eutectic6337/soldering-exercise/i/PCB back.jpg

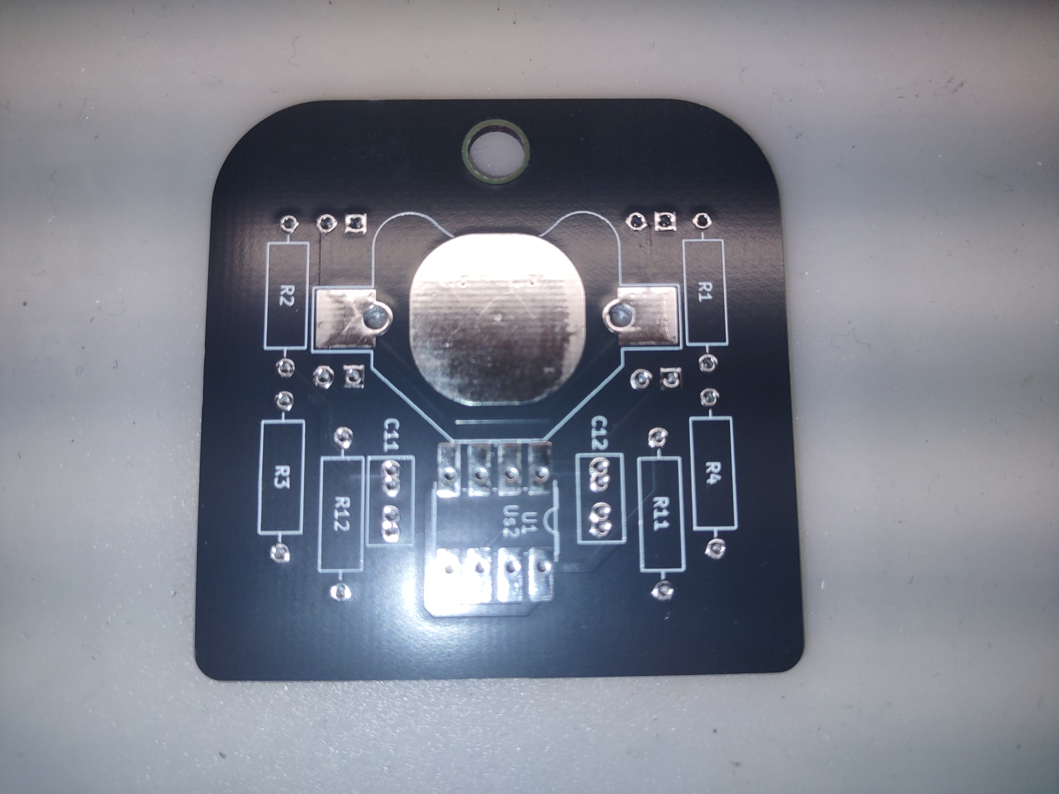
i/PCB back.jpg
