eutectic6337/soldering-exercise/i/PCB front.jpg

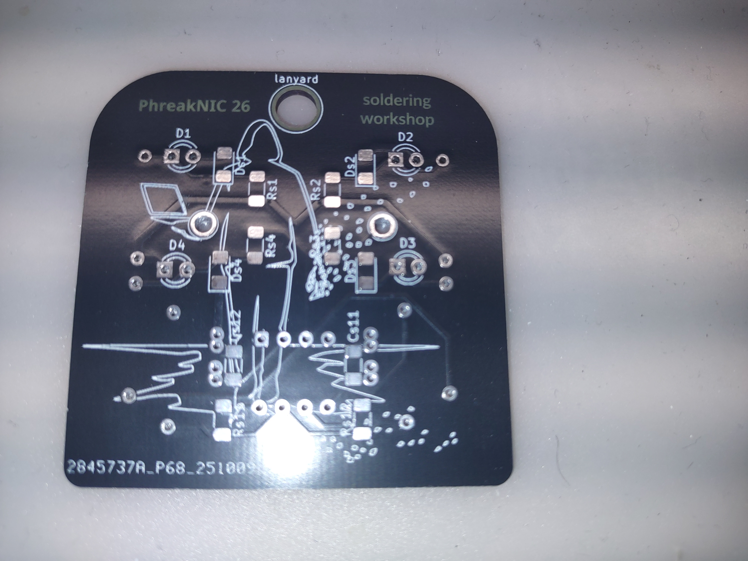
i/PCB front.jpg
