eutectic6337/soldering-exercise/i/SMD 555 front.png

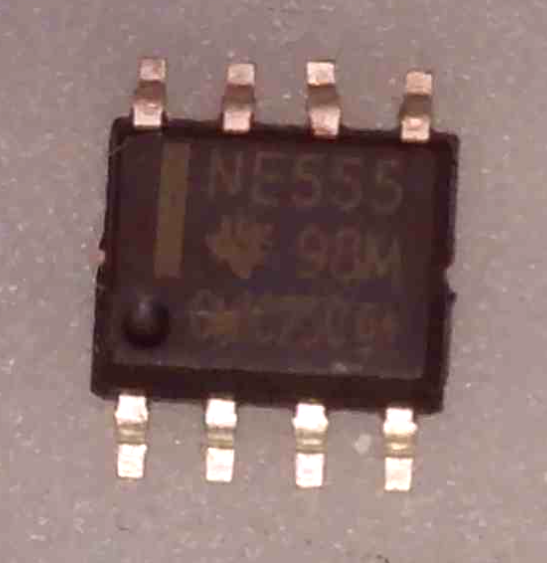
i/SMD 555 front.png
