eutectic6337/soldering-exercise/i/SMD 555 side.png

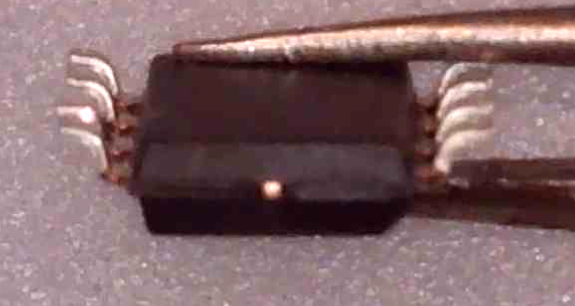
i/SMD 555 side.png
