eutectic6337/soldering-exercise/i/SMD 555 tape.png

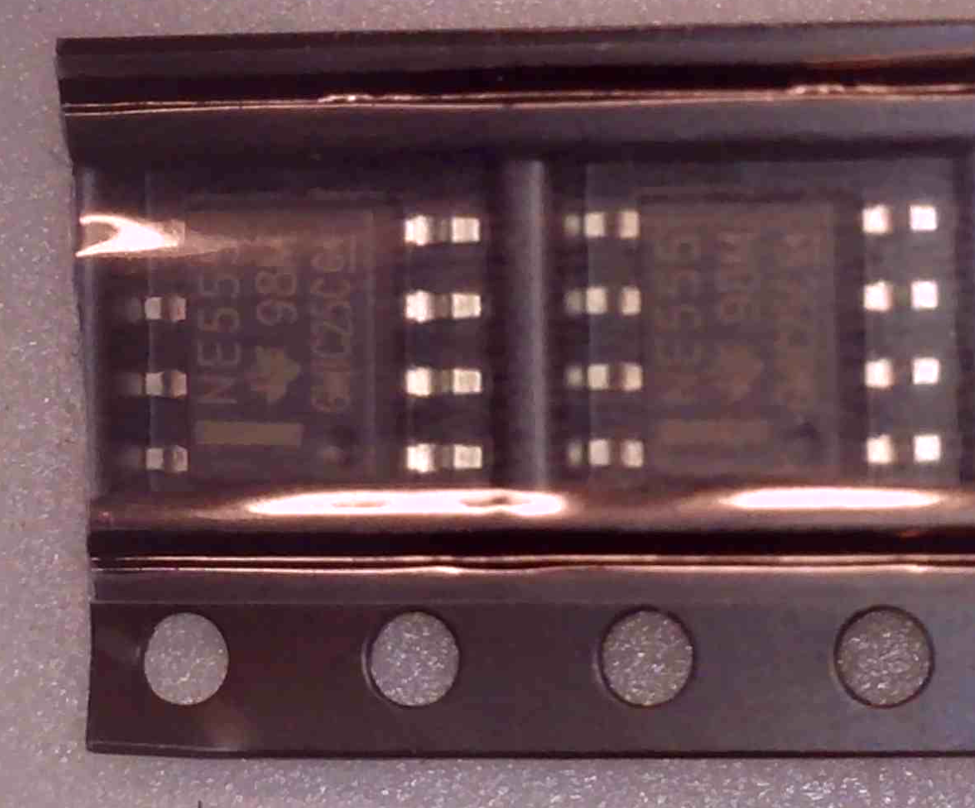
i/SMD 555 tape.png
