eutectic6337/soldering-exercise/i/SMD LED angled.png

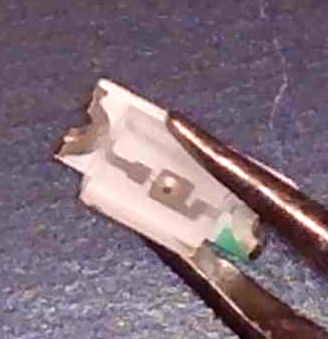
i/SMD LED angled.png
