eutectic6337/soldering-exercise/i/SMD LED back.png

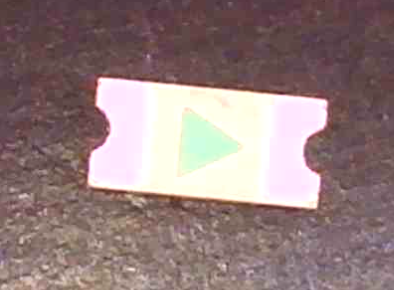
i/SMD LED back.png
