eutectic6337/soldering-exercise/i/SMD LED front.png

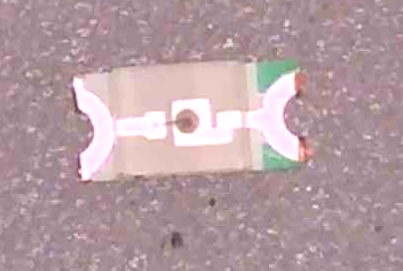
i/SMD LED front.png
