eutectic6337/soldering-exercise/i/SMD LED side.png

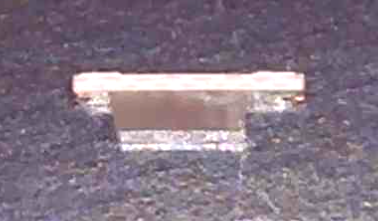
i/SMD LED side.png
