eutectic6337/soldering-exercise/i/SMD resistor 22R tape.png

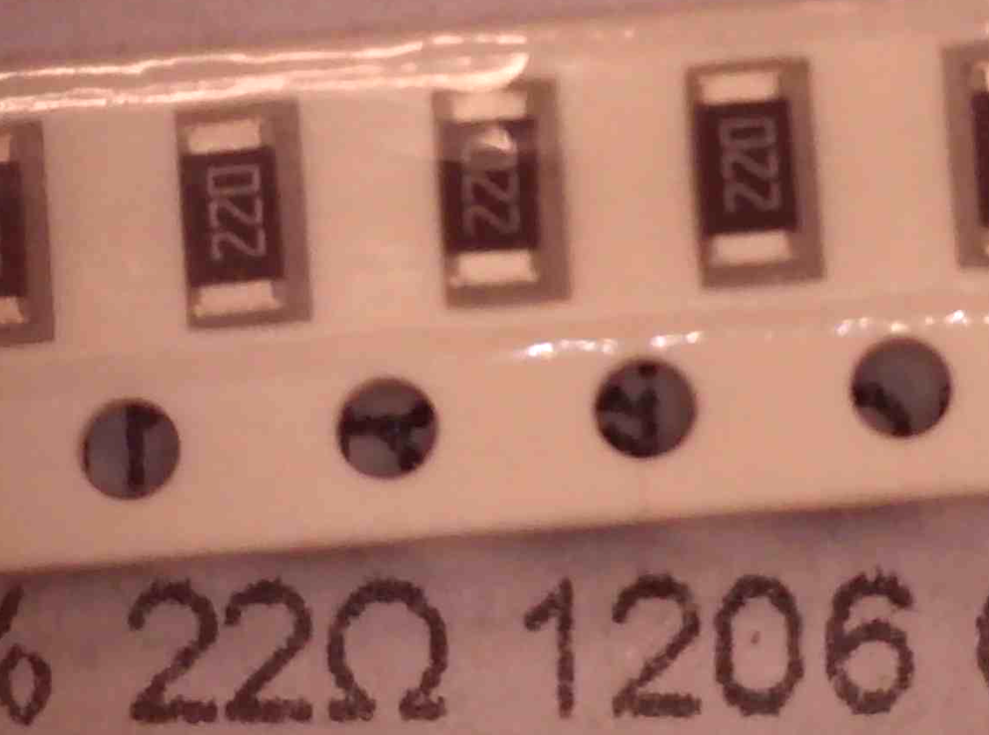
i/SMD resistor 22R tape.png
