eutectic6337/soldering-exercise/i/SMD resistor 62R front.png

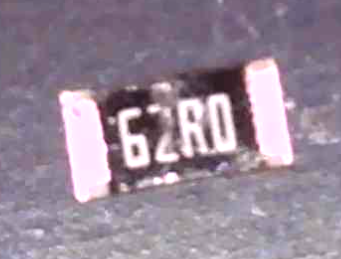
i/SMD resistor 62R front.png
