eutectic6337/soldering-exercise/i/SMD resistor 62R tape.png

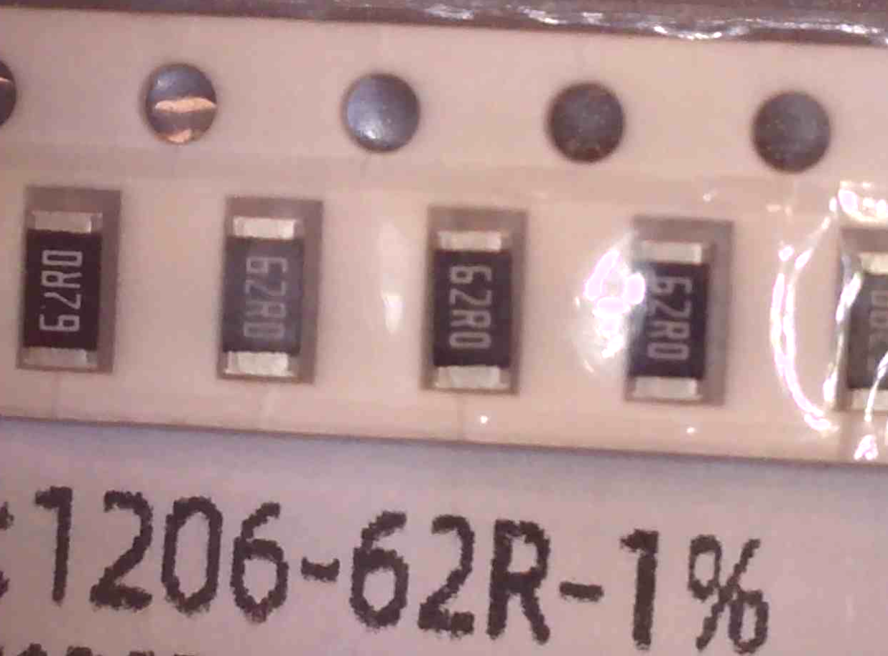
i/SMD resistor 62R tape.png
