eutectic6337/soldering-exercise/i/SMD resistor back.png

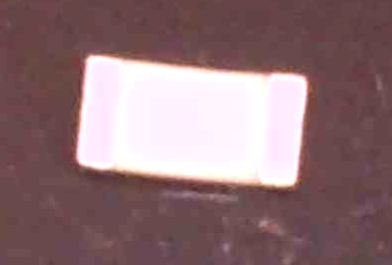
i/SMD resistor back.png
