eutectic6337/soldering-exercise/i/SMD resistor side.png

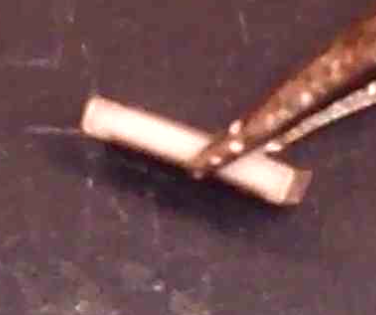
i/SMD resistor side.png
