eutectic6337/soldering-exercise/i/THT 555 front.png

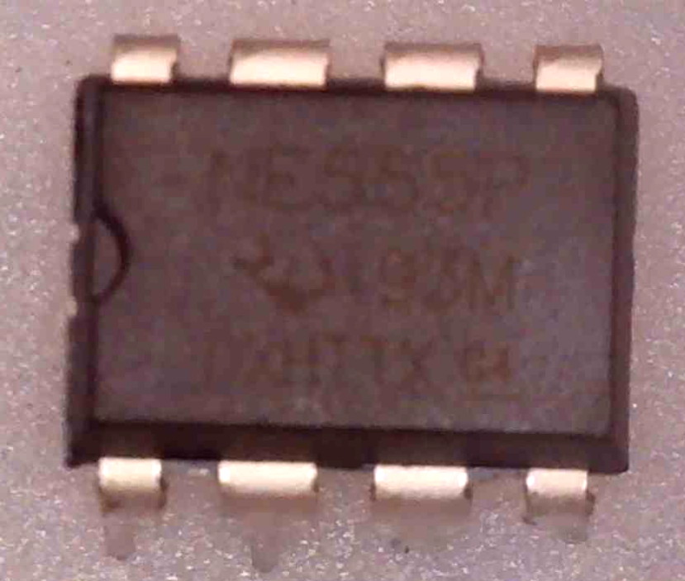
i/THT 555 front.png
