eutectic6337/soldering-exercise/i/THT 555 side.png

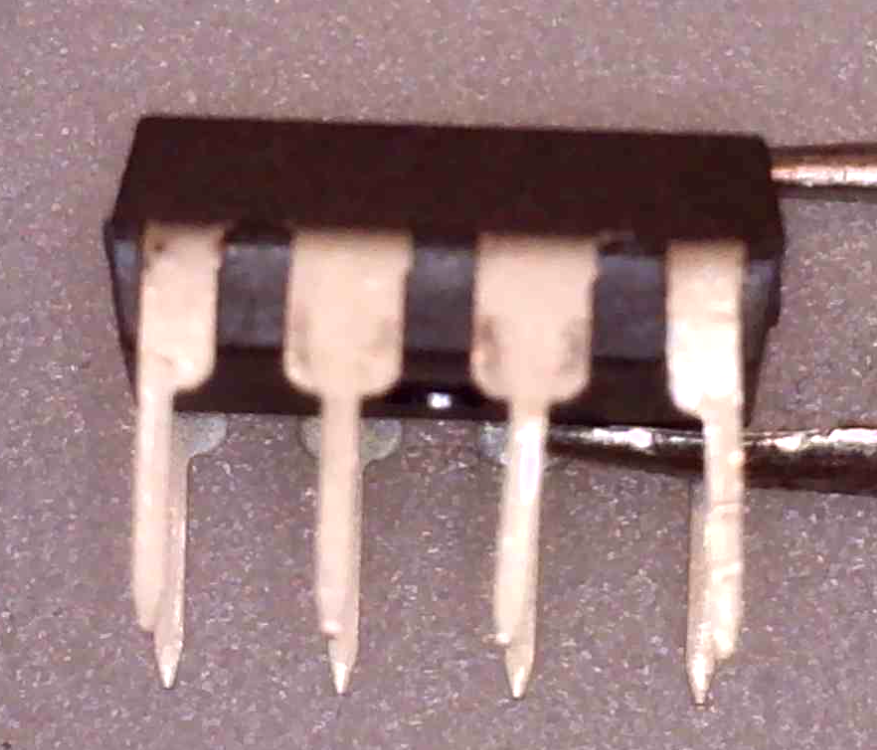
i/THT 555 side.png
