eutectic6337/soldering-exercise/i/THT LED blue.jpg

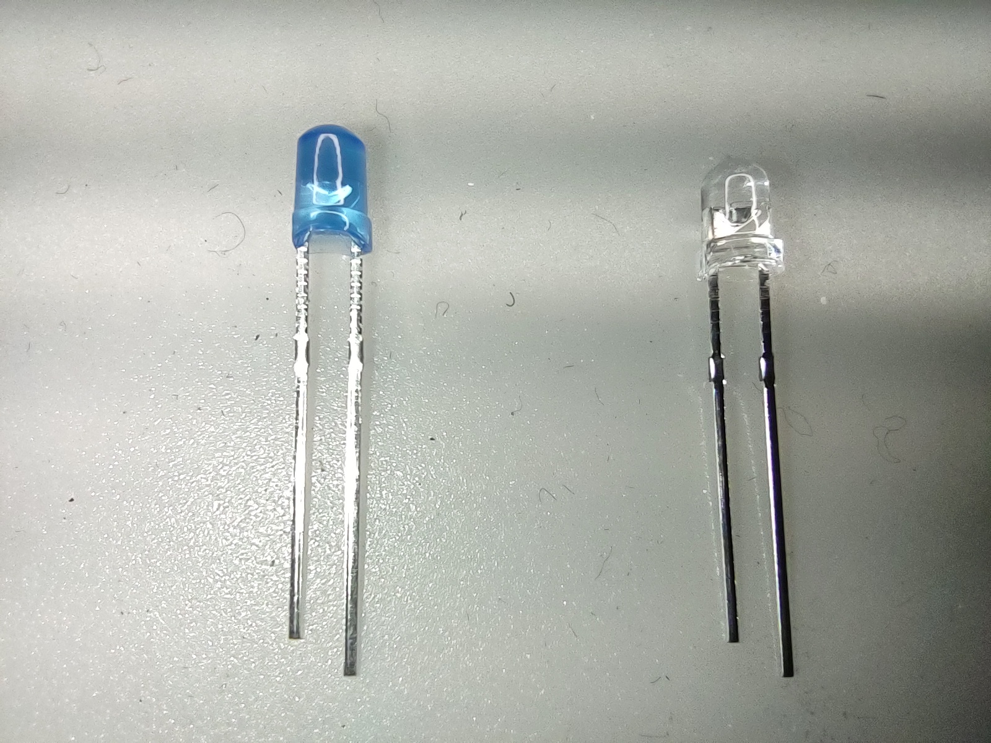
i/THT LED blue.jpg
