eutectic6337/soldering-exercise/i/THT LED green.jpg

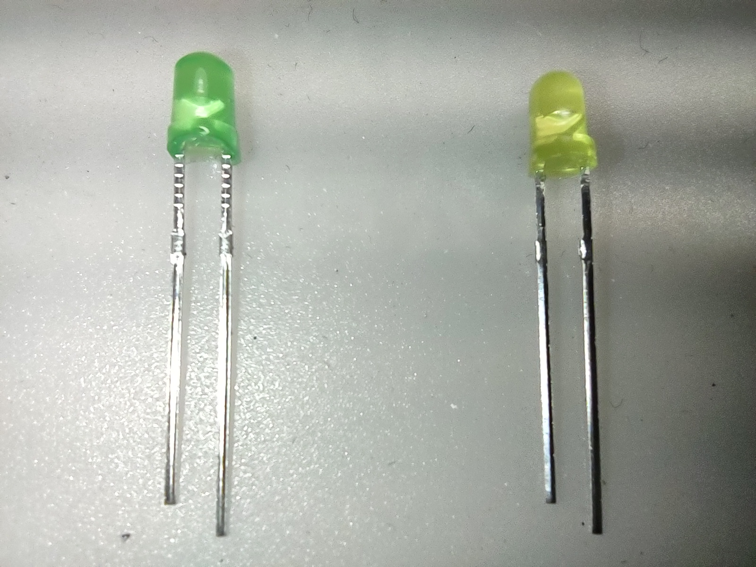
i/THT LED green.jpg
