eutectic6337/soldering-exercise/i/THT LED red close.png

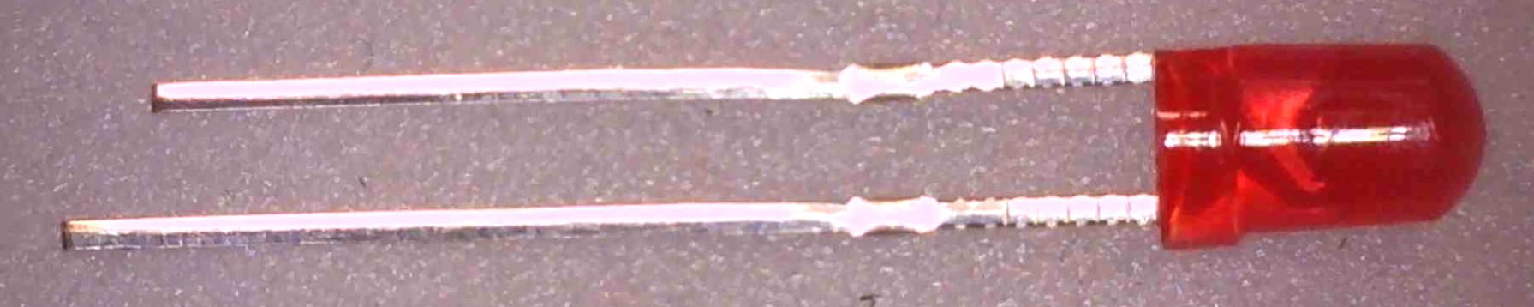
i/THT LED red close.png
