eutectic6337/soldering-exercise/i/THT LED red.jpg

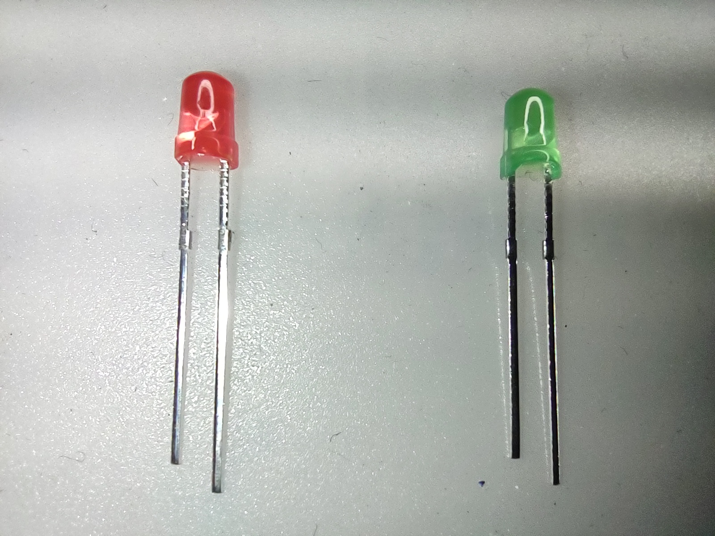
i/THT LED red.jpg
