eutectic6337/soldering-exercise/i/THT LEDs x5.jpg

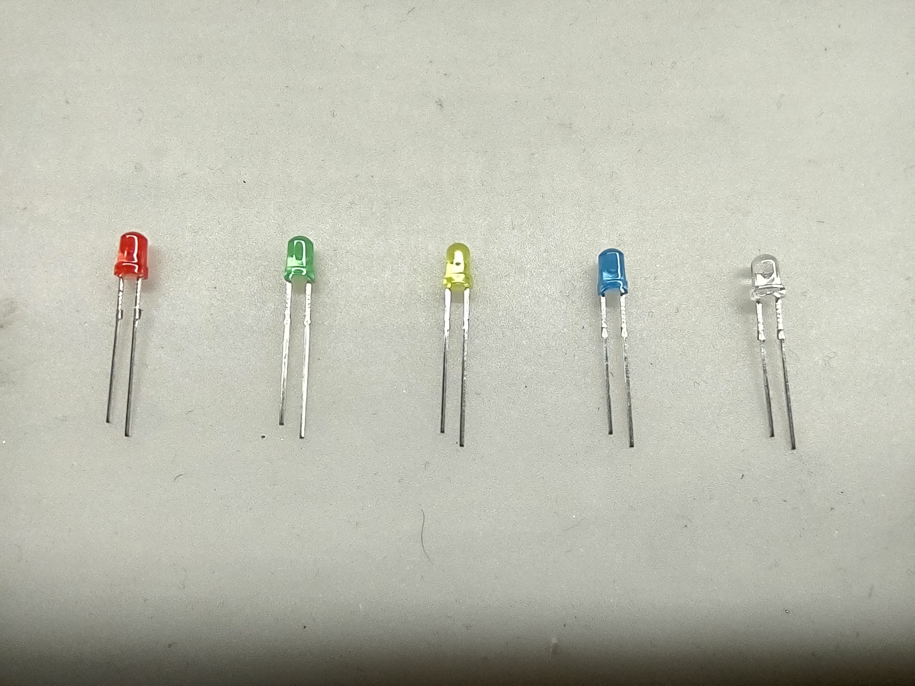
i/THT LEDs x5.jpg
