eutectic6337/soldering-exercise/i/THT resistor 62R.jpg

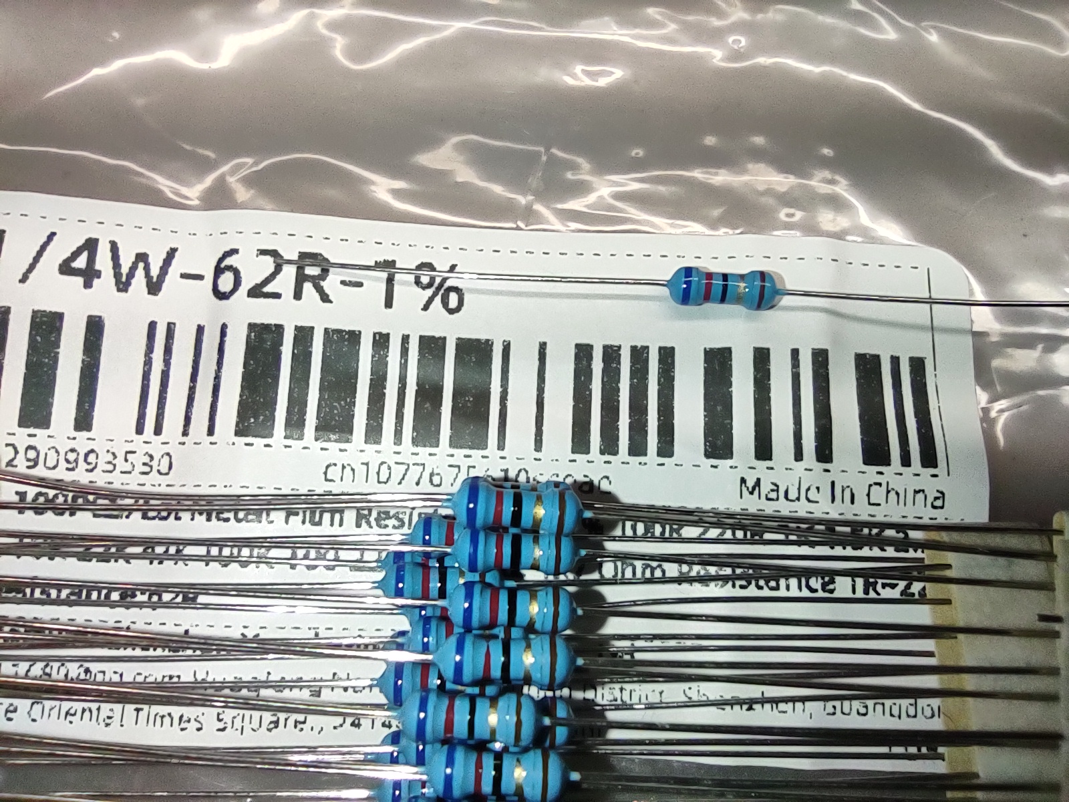
i/THT resistor 62R.jpg
