eutectic6337/soldering-exercise/i/THT resistor 270R.png

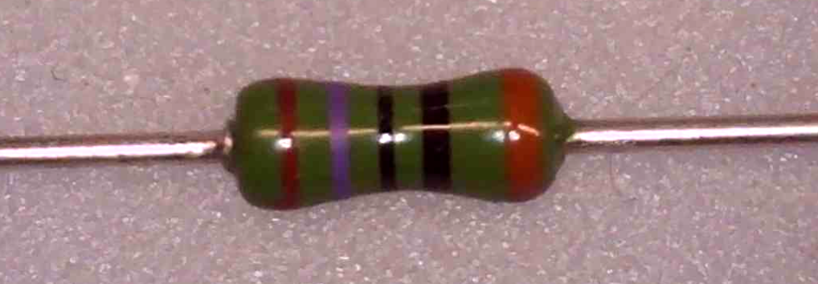
i/THT resistor 270R.png
