eutectic6337/soldering-exercise/i/THT resistor 562K.png

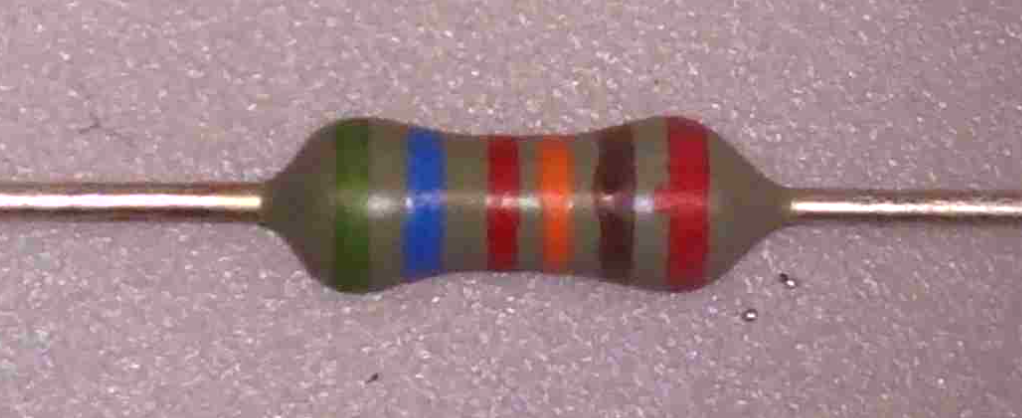
i/THT resistor 562K.png
